Batterhead221/dbg_mcu/Outputs/IMG/FAB_B.jpeg

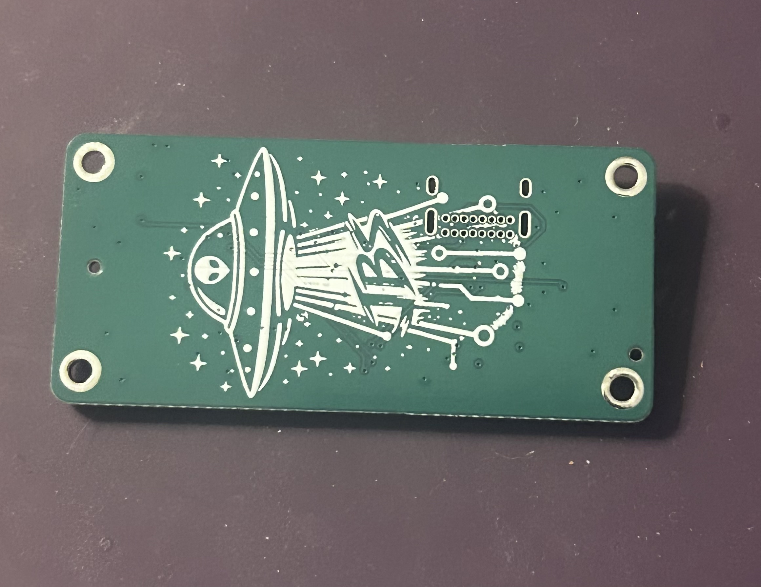
Outputs/IMG/FAB_B.jpeg
