Batterhead221/dbg_mcu/Outputs/IMG/FAB_T.jpeg

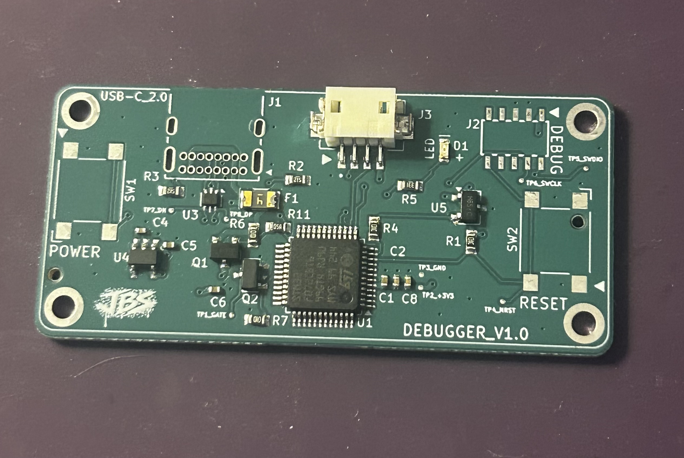
Outputs/IMG/FAB_T.jpeg
