Batterhead221/dbg_mcu/Outputs/IMG/3D_B.png

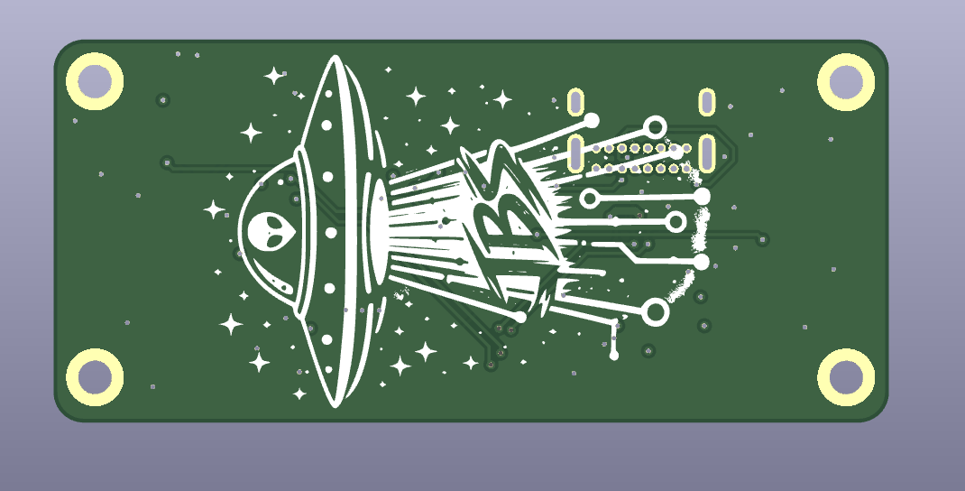
Outputs/IMG/3D_B.png
