Batterhead221/dbg_mcu/Outputs/IMG/3D_T.png

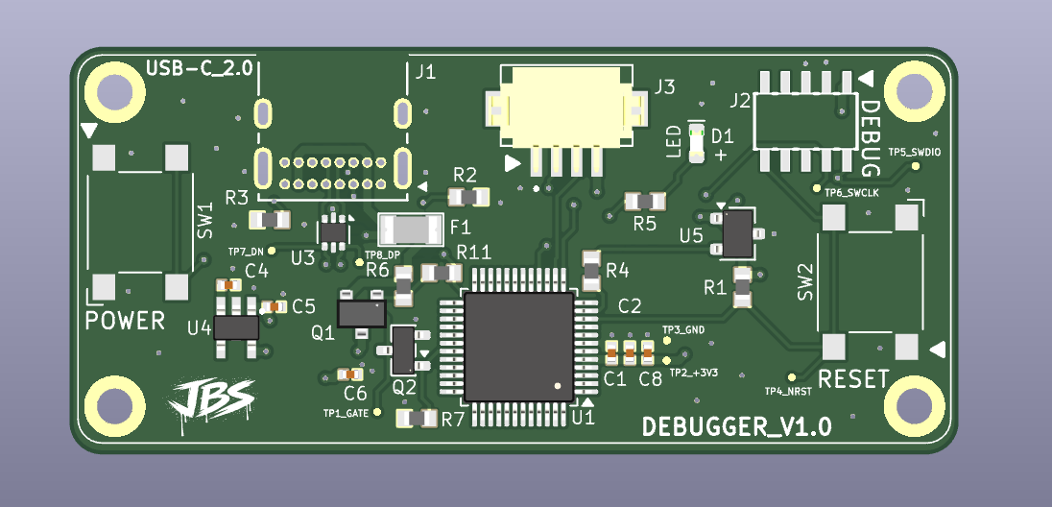
Outputs/IMG/3D_T.png
