Batterhead221/dbg_mcu/Outputs/IMG/HERO.png

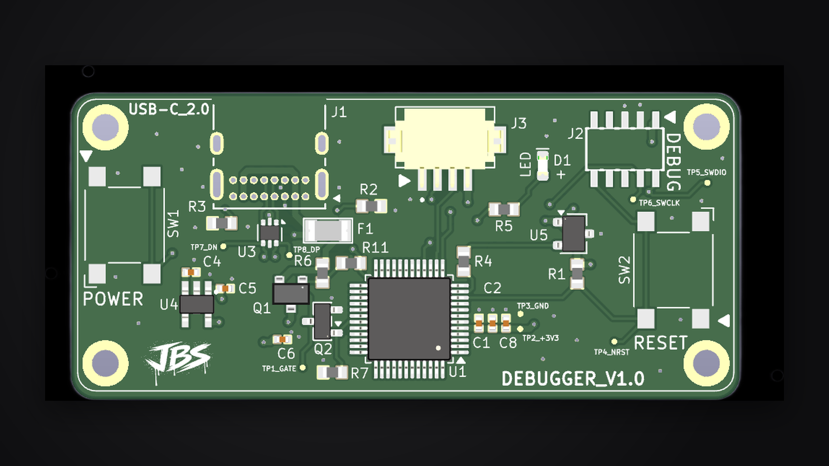
Outputs/IMG/HERO.png
