Batterhead221/dbg_mcu/Outputs/IMG/L1-SIG.png

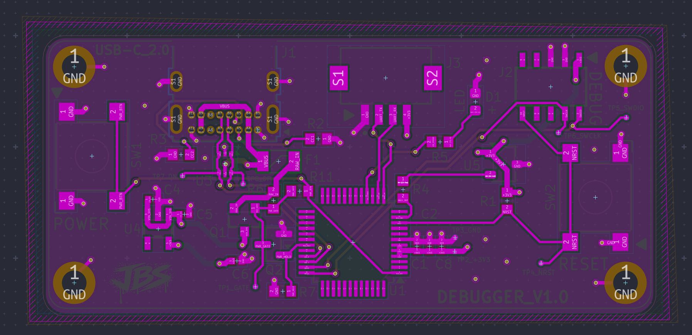
Outputs/IMG/L1-SIG.png
