Batterhead221/dbg_mcu/Outputs/IMG/L2-GND.png

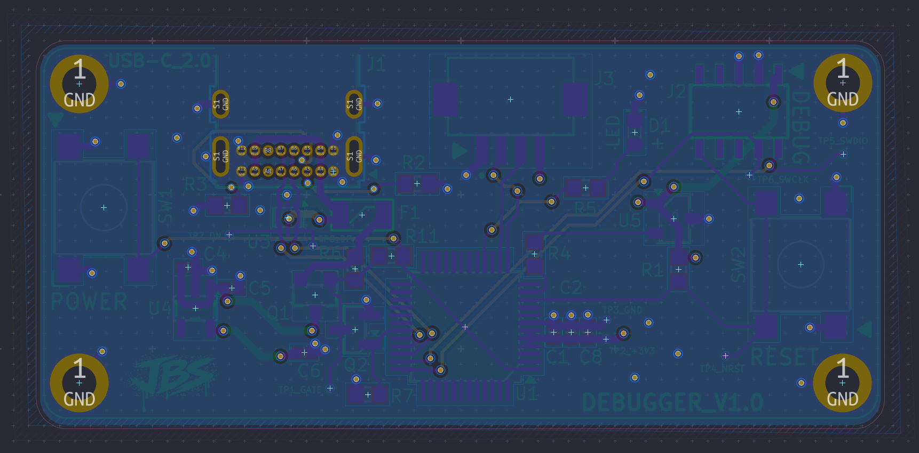
Outputs/IMG/L2-GND.png
