Batterhead221/dbg_mcu/Outputs/IMG/L3-PWR.png

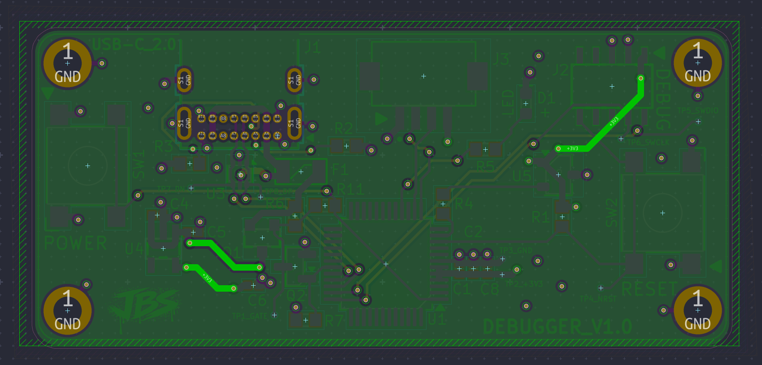
Outputs/IMG/L3-PWR.png
