Batterhead221/dbg_mcu/Outputs/IMG/L4-SIG.png

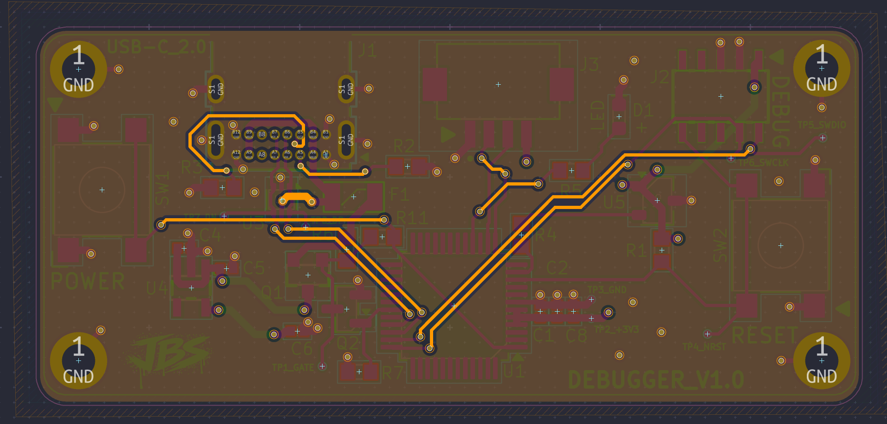
Outputs/IMG/L4-SIG.png
