Batterhead221/dbg_mcu/Outputs/IMG/SCHEMATIC.png

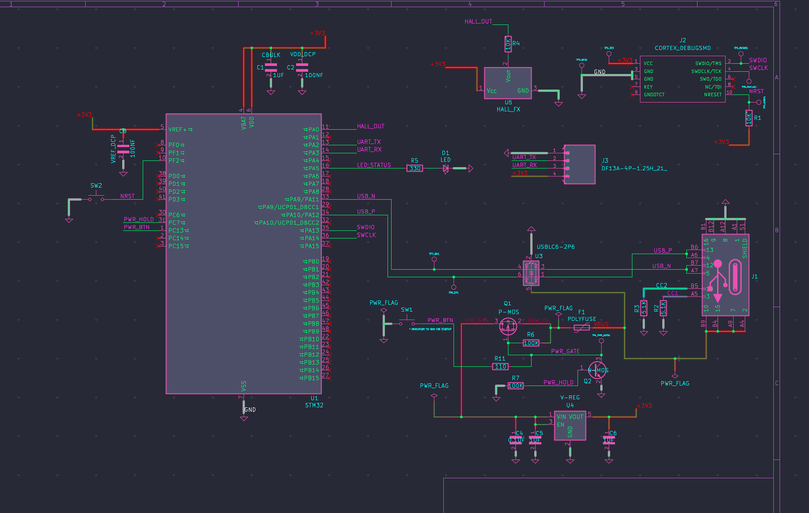
Outputs/IMG/SCHEMATIC.png
