Batterhead221/dbg_mcu/Outputs/IMG/SOCIAL.png

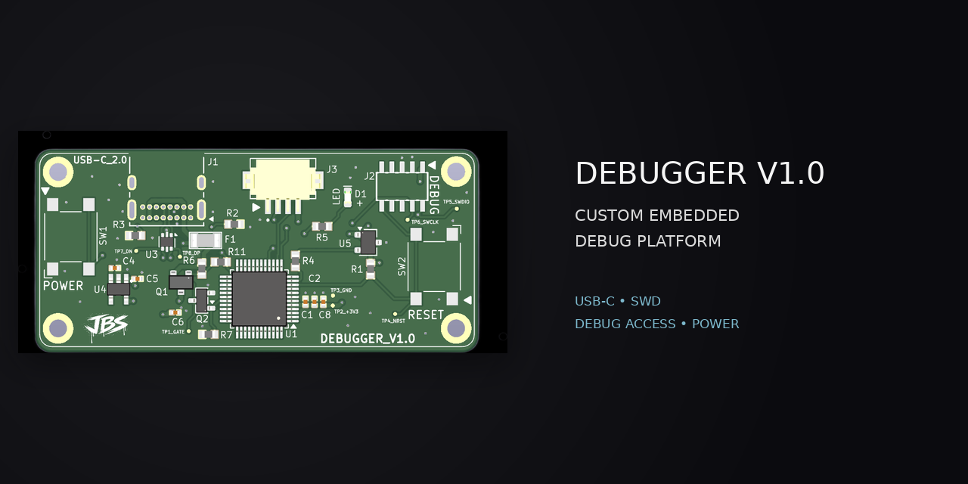
Outputs/IMG/SOCIAL.png
